knurtz/TinySoundV2/Code/TinySound/TS_sine.c

#include "TS_sine.h"

const int16_t dac_buffer[960] = {
    298, 298, 595, 595, 893, 893, 1191, 1191, 1489, 1489, 1786, 1786, 2083, 2083, 2379, 2379, 2676, 2676, 2971, 2971, 
    3267, 3267, 3561, 3561, 3855, 3855, 4149, 4149, 4441, 4441, 4733, 4733, 5024, 5024, 5315, 5315, 5604, 5604, 5892, 5892, 
    6180, 6180, 6466, 6466, 6751, 6751, 7035, 7035, 7318, 7318, 7600, 7600, 7880, 7880, 8159, 8159, 8436, 8436, 8712, 8712, 
    8987, 8987, 9260, 9260, 9532, 9532, 9801, 9801, 10070, 10070, 10336, 10336, 10601, 10601, 10863, 10863, 11124, 11124, 11383, 11383, 
    11641, 11641, 11896, 11896, 12149, 12149, 12400, 12400, 12649, 12649, 12895, 12895, 13140, 13140, 13382, 13382, 13622, 13622, 13860, 13860, 
    14095, 14095, 14328, 14328, 14558, 14558, 14786, 14786, 15011, 15011, 15234, 15234, 15454, 15454, 15672, 15672, 15887, 15887, 16099, 16099, 
    16308, 16308, 16515, 16515, 16719, 16719, 16919, 16919, 17117, 17117, 17312, 17312, 17504, 17504, 17694, 17694, 17880, 17880, 18063, 18063, 
    18242, 18242, 18419, 18419, 18593, 18593, 18763, 18763, 18930, 18930, 19094, 19094, 19255, 19255, 19412, 19412, 19566, 19566, 19717, 19717, 
    19864, 19864, 20008, 20008, 20149, 20149, 20286, 20286, 20419, 20419, 20550, 20550, 20676, 20676, 20799, 20799, 20919, 20919, 21034, 21034, 
    21147, 21147, 21255, 21255, 21360, 21360, 21462, 21462, 21559, 21559, 21653, 21653, 21743, 21743, 21830, 21830, 21913, 21913, 21992, 21992, 
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
    -21913, -21913, -21830, -21830, -21743, -21743, -21653, -21653, -21559, -21559, -21462, -21462, -21360, -21360, -21255, -21255, -21147, -21147, -21034, -21034, 
    -20919, -20919, -20799, -20799, -20676, -20676, -20550, -20550, -20419, -20419, -20286, -20286, -20149, -20149, -20008, -20008, -19864, -19864, -19717, -19717, 
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
};
